signal-slot/usb-imx-rt1170-evk-reset/software/firmware/build.rs

use std::env;
use std::fs::File;
use std::io::Write;
use std::path::PathBuf;

fn main() {
    // cortex-m-rt's link.x does `INCLUDE memory.x`. Copy memory.x into OUT_DIR
    // and tell the linker to search there so the include resolves.
    let out = PathBuf::from(env::var_os("OUT_DIR").unwrap());
    File::create(out.join("memory.x"))
        .unwrap()
        .write_all(include_bytes!("memory.x"))
        .unwrap();
    println!("cargo:rustc-link-search={}", out.display());

    println!("cargo:rerun-if-changed=memory.x");
    println!("cargo:rerun-if-changed=build.rs");
}
